elbosso/esp8266ntpledmatrixclock/marquee_font.h

#ifndef MARQUEE_FONT_H
#define MARQUEE_FONT_H

/** 
 * 8x8 monochrome bitmap fonts for rendering
 * Author: Daniel Hepper <daniel@hepper.net>
 * 
 * License: Public Domain
 * 
 * Based on:
 * // Summary: font8x8.h
 * // 8x8 monochrome bitmap fonts for rendering
 * //
 * // Author:
 * //     Marcel Sondaar
 * //     International Business Machines (public domain VGA fonts)
 * //
 * // License:
 * //     Public Domain
 * 
 * Fetched from: http://dimensionalrift.homelinux.net/combuster/mos3/?p=viewsource&file=/modules/gfx/font8_8.asm
 **/
//found at: https://github.com/dhepper/font8x8

byte marqueeFont[226][8] = { 
  {0x00,0x00,0x00,0x00,0x00,0x00,0x00,0x00},  // U+0020 (space)
  {0x18,0x3c,0x3c,0x18,0x18,0x00,0x18,0x00},  // U+0021 (!)
  {0x36,0x36,0x00,0x00,0x00,0x00,0x00,0x00},  // U+0022 (")
  {0x36,0x36,0x7f,0x36,0x7f,0x36,0x36,0x00},  // U+0023 (#)
  {0x0c,0x1f,0x30,0x1e,0x03,0x3e,0x0c,0x00},  // U+0024 ($)
  {0x00,0x63,0x66,0x0c,0x18,0x33,0x63,0x00},  // U+0025 (%)
  {0x1c,0x36,0x1c,0x3b,0x6e,0x66,0x3b,0x00},  // U+0026 (&)
  {0x06,0x06,0x0c,0x00,0x00,0x00,0x00,0x00},  // U+0027 (')
  {0x06,0x0c,0x18,0x18,0x18,0x0c,0x06,0x00},  // U+0028 (()
  {0x18,0x0c,0x06,0x06,0x06,0x0c,0x18,0x00},  // U+0029 ())
  {0x00,0x66,0x3c,0xff,0x3c,0x66,0x00,0x00},  // U+002A (*)
  {0x00,0x0c,0x0c,0x3f,0x0c,0x0c,0x00,0x00},  // U+002B (+)
  {0x00,0x00,0x00,0x00,0x00,0x06,0x06,0x0c},  // U+002C (,)
  {0x00,0x00,0x00,0x3f,0x00,0x00,0x00,0x00},  // U+002D (-)
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
  {0x00,0x07,0x00,0x33,0x33,0x1f,0x03,0x3e},  // U+00FD (y aigu)
  {0x00,0x00,0x60,0x7c,0x66,0x7c,0x60,0x00},  // U+00FE (thorn)
  {0x00,0x33,0x00,0x33,0x33,0x1f,0x03,0x3e},  // U+00FF (y umlaut)

};    // {}, //

#endif /* MARQUEE_FONT_H */
