elbosso/esp8266ntpledmatrixclock/marquee_font1.h

#ifndef MARQUEE_FONT1_H
#define MARQUEE_FONT1_H
//https://www.mikrocontroller.net/topic/54860
byte marqueeFont1[226][8] = {
{0x00,0x00,0x00,0x00,0x00,0x00,0x00,0x00},  // U+0020 (space)
{0x04,0x0E,0x0E,0x04,0x04,0x00,0x04,0x00},  // U+0021 (!)        
{0x1B,0x1B,0x12,0x00,0x00,0x00,0x00,0x00},  // U+0022 (")        
{0x00,0x0A,0x1F,0x0A,0x0A,0x1F,0x0A,0x00},  // U+0023 (#)        
{0x08,0x0E,0x10,0x0C,0x02,0x1C,0x04,0x00},  // U+0024 ($)        
{0x19,0x19,0x02,0x04,0x08,0x13,0x13,0x00},  // U+0025 (%)        
{0x08,0x14,0x14,0x08,0x15,0x12,0x0D,0x00},  // U+0026 (&)        
{0x0C,0x0C,0x08,0x00,0x00,0x00,0x00,0x00},  // U+0027 (')        
{0x04,0x08,0x08,0x08,0x08,0x08,0x04,0x00},  // U+0028 (()        
{0x08,0x04,0x04,0x04,0x04,0x04,0x08,0x00},  // U+0029 ())        
{0x00,0x0A,0x0E,0x1F,0x0E,0x0A,0x00,0x00},  // U+002A (*)        
{0x00,0x04,0x04,0x1F,0x04,0x04,0x00,0x00},  // U+002B (+)        
{0x00,0x00,0x00,0x00,0x00,0x0C,0x0C,0x08},  // U+002C (,)        
{0x00,0x00,0x00,0x1F,0x00,0x00,0x00,0x00},  // U+002D (-)        
{0x00,0x00,0x00,0x00,0x00,0x0C,0x0C,0x00},  // U+002E (.)        
{0x00,0x01,0x02,0x04,0x08,0x10,0x00,0x00},  // U+002F (/)        
{0x0E,0x11,0x13,0x15,0x19,0x11,0x0E,0x00},  // U+0030 (0)        
{0x04,0x0C,0x04,0x04,0x04,0x04,0x0E,0x00},  // U+0031 (1)        
{0x0E,0x11,0x01,0x06,0x08,0x10,0x1F,0x00},  // U+0032 (2)        
{0x0E,0x11,0x01,0x0E,0x01,0x11,0x0E,0x00},  // U+0033 (3)        
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
  {0x00,0x00,0x08,0x0e,0x09,0x0e,0x08,0x00},  // U+00FE (thorn)
  {0x00,0x09,0x00,0x09,0x09,0x07,0x01,0x0e},  // U+00FF (y umlaut)

                      // (the font does not contain any lower case letters. you can add your own.)
                  };    // {}, // 

#endif /* MARQUEE_FONT1_H */
