elbosso/esp8266ntpledmatrixclock/clock_font.h

#ifndef CLOCK_FONT_H
#define CLOCK_FONT_H

// This is the font definition. You can use http://gurgleapps.com/tools/matrix to create your own font or sprites.
// If you like the font feel free to use it. I created it myself and donate it to the public domain.
byte clockfont[95][8] = { {0,0,0,0,0,0,0,0}, // SPACE
                     {0x00,0x38,0x44,0x4d,0x54,0x65,0x44,0x38}, // 0
                     {0x00,0x08,0x18,0x29,0x48,0x09,0x08,0x1c}, // 1
                     {0x00,0x38,0x44,0x05,0x04,0x39,0x40,0x7c}, // 2
                     {0x00,0x38,0x44,0x05,0x18,0x05,0x44,0x38}, // 3
                     {0x00,0x48,0x48,0x49,0x48,0x7d,0x08,0x08}, // 4
                     {0x00,0x7c,0x40,0x41,0x78,0x05,0x44,0x38}, // 5
                     {0x00,0x38,0x40,0x41,0x78,0x45,0x44,0x38}, // 6
                     {0x00,0x7c,0x04,0x05,0x08,0x09,0x10,0x10}, // 7
                     {0x00,0x38,0x44,0x45,0x38,0x45,0x44,0x38}, // 8
                     {0x00,0x38,0x44,0x45,0x3c,0x05,0x04,0x78}, // 9
/*                     {0x10,0x18,0x18,0x18,0x18,0x00,0x18,0x18}, // EXCL
                     {0x28,0x28,0x08,0x00,0x00,0x00,0x00,0x00}, // QUOT
                     {0x00,0x0a,0x7f,0x14,0x28,0xfe,0x50,0x00}, // #
                     {0x10,0x38,0x54,0x70,0x1c,0x54,0x38,0x10}, // $
                     {0x00,0x60,0x66,0x08,0x10,0x66,0x06,0x00}, // %
                     {0,0,0,0,0,0,0,0}, // &
                     {0x00,0x10,0x18,0x18,0x08,0x00,0x00,0x00}, // '
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
                     {0x00,0x42,0x42,0x62,0x52,0x4a,0x46,0x42}, // N
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
                      // (the font does not contain any lower case letters. you can add your own.)
                  };    // {}, // 

#endif /* CLOCK_FONT_H */
